carlren/zwift-foot-pod/recordings/20261006T043211_628804Z_collection-validation/imu.csv

sequence | device_us | elapsed_us | received_utc | received_monotonic_ns | gx_raw | gy_raw | gz_raw | ax_raw | ay_raw | az_raw | gx_dps | gy_dps | gz_dps | ax_g | ay_g | az_g
10037 | 96027343 | 0 | 2026-10-06T04:32:17.915393+00:00 | 214157936814735 | 66 | -67 | -15 | -966 | -1903 | 3619 | 2.31 | -2.345 | -0.525 | -0.235704 | -0.464332 | 0.883036
10038 | 96037109 | 9766 | 2026-10-06T04:32:17.916443+00:00 | 214157937852882 | 59 | -66 | -18 | -966 | -1914 | 3617 | 2.065 | -2.31 | -0.63 | -0.235704 | -0.467016 | 0.882548
10039 | 96047851 | 20508 | 2026-10-06T04:32:17.916978+00:00 | 214157938381596 | 59 | -66 | -17 | -956 | -1927 | 3623 | 2.065 | -2.31 | -0.595 | -0.233264 | -0.470188 | 0.884012
10040 | 96052734 | 25391 | 2026-10-06T04:32:17.917451+00:00 | 214157938868801 | 63 | -67 | -16 | -963 | -1914 | 3622 | 2.205 | -2.345 | -0.56 | -0.234972 | -0.467016 | 0.883768
10041 | 96062500 | 35157 | 2026-10-06T04:32:17.918092+00:00 | 214157939499047 | 67 | -67 | -15 | -965 | -1908 | 3614 | 2.345 | -2.345 | -0.525 | -0.23546 | -0.465552 | 0.881816
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
