carlren/zwift-foot-pod/recordings/20261006T043904_071612Z_collection-validation/imu.csv

sequence | device_us | elapsed_us | received_utc | received_monotonic_ns | gx_raw | gy_raw | gz_raw | ax_raw | ay_raw | az_raw | gx_dps | gy_dps | gz_dps | ax_g | ay_g | az_g
52838 | 503707031 | 0 | 2026-10-06T04:39:05.589423+00:00 | 214565610826059 | 64 | -68 | -13 | 4 | -3107 | 2785 | 2.24 | -2.38 | -0.455 | 0.000976 | -0.758108 | 0.67954
52839 | 503717773 | 10742 | 2026-10-06T04:39:05.589811+00:00 | 214565611208976 | 67 | -67 | -15 | -1 | -3120 | 2790 | 2.345 | -2.345 | -0.525 | -0.000244 | -0.76128 | 0.68076
52840 | 503727539 | 20508 | 2026-10-06T04:39:05.590080+00:00 | 214565611477507 | 63 | -69 | -16 | 8 | -3127 | 2787 | 2.205 | -2.415 | -0.56 | 0.001952 | -0.762988 | 0.680028
52841 | 503737304 | 30273 | 2026-10-06T04:39:05.591249+00:00 | 214565612645821 | 66 | -65 | -14 | 1 | -3127 | 2783 | 2.31 | -2.275 | -0.49 | 0.000244 | -0.762988 | 0.679052
52842 | 503747070 | 40039 | 2026-10-06T04:39:05.591508+00:00 | 214565612904186 | 69 | -67 | -13 | 1 | -3121 | 2804 | 2.415 | -2.345 | -0.455 | 0.000244 | -0.761524 | 0.684176
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
