carlren/zwift-foot-pod/recordings/20261006T055524_775644Z_collection-validation/imu.csv

sequence | device_us | elapsed_us | received_utc | received_monotonic_ns | gx_raw | gy_raw | gz_raw | ax_raw | ay_raw | az_raw | gx_dps | gy_dps | gz_dps | ax_g | ay_g | az_g
22132 | 211217773 | 0 | 2026-10-06T05:55:31.658095+00:00 | 219151679488468 | 69 | -70 | -19 | 547 | -706 | 4133 | 2.415 | -2.45 | -0.665 | 0.133468 | -0.172264 | 1.008452
22133 | 211227539 | 9766 | 2026-10-06T05:55:31.660020+00:00 | 219151681409835 | 65 | -70 | -18 | 558 | -703 | 4147 | 2.275 | -2.45 | -0.63 | 0.136152 | -0.171532 | 1.011868
22134 | 211237304 | 19531 | 2026-10-06T05:55:31.660238+00:00 | 219151681626893 | 64 | -60 | -13 | 543 | -707 | 4147 | 2.24 | -2.1 | -0.455 | 0.132492 | -0.172508 | 1.011868
22135 | 211247070 | 29297 | 2026-10-06T05:55:31.660370+00:00 | 219151681756602 | 66 | -60 | -11 | 521 | -707 | 4116 | 2.31 | -2.1 | -0.385 | 0.127124 | -0.172508 | 1.004304
22136 | 211257812 | 40039 | 2026-10-06T05:55:31.661969+00:00 | 219151683357473 | 65 | -64 | -12 | 525 | -706 | 4108 | 2.275 | -2.24 | -0.42 | 0.1281 | -0.172264 | 1.002352
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
