carlren/zwift-foot-pod/recordings/20261006T140140_892176Z_collection-validation/imu.csv

sequence | device_us | elapsed_us | received_utc | received_monotonic_ns | gx_raw | gy_raw | gz_raw | ax_raw | ay_raw | az_raw | gx_dps | gy_dps | gz_dps | ax_g | ay_g | az_g
14012 | 133865234 | 0 | 2026-10-06T14:01:43.888239+00:00 | 248323909631397 | 63 | -66 | -17 | 794 | 390 | 4163 | 2.205 | -2.31 | -0.595 | 0.193736 | 0.09516 | 1.015772
14013 | 133875000 | 9766 | 2026-10-06T14:01:43.890077+00:00 | 248323911469225 | 65 | -68 | -18 | 803 | 390 | 4160 | 2.275 | -2.38 | -0.63 | 0.195932 | 0.09516 | 1.01504
14014 | 133885742 | 20508 | 2026-10-06T14:01:43.890271+00:00 | 248323911680274 | 65 | -68 | -18 | 800 | 395 | 4167 | 2.275 | -2.38 | -0.63 | 0.1952 | 0.09638 | 1.016748
14015 | 133895507 | 30273 | 2026-10-06T14:01:43.890513+00:00 | 248323911917029 | 63 | -65 | -19 | 806 | 393 | 4171 | 2.205 | -2.275 | -0.665 | 0.196664 | 0.095892 | 1.017724
14016 | 133900390 | 35156 | 2026-10-06T14:01:43.893015+00:00 | 248323914401347 | 64 | -64 | -18 | 798 | 392 | 4172 | 2.24 | -2.24 | -0.63 | 0.194712 | 0.095648 | 1.017968
14017 | 133910156 | 44922 | 2026-10-06T14:01:43.935210+00:00 | 248323956604450 | 64 | -68 | -19 | 799 | 391 | 4159 | 2.24 | -2.38 | -0.665 | 0.194956 | 0.095404 | 1.014796
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
